beitong95/SENSELET_PLUSPLUS/Printed Circuit Board/T board/T board Schematic.png

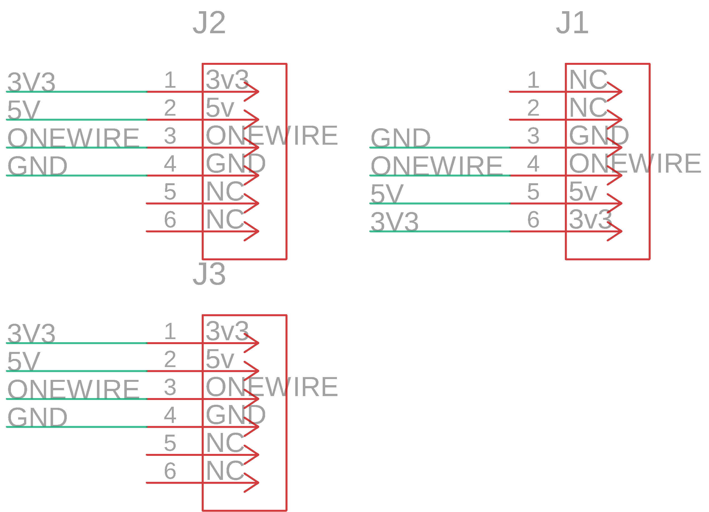
Printed Circuit Board/T board/T board Schematic.png
