beitong95/SENSELET_PLUSPLUS/3D Printed Closure/airflow sensor.png

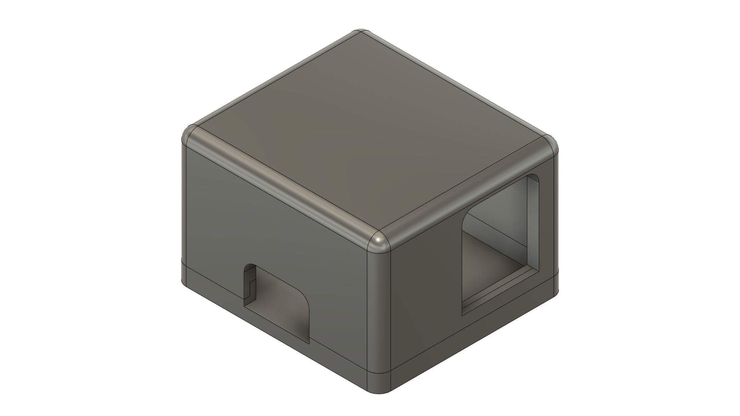
3D Printed Closure/airflow sensor.png
