beitong95/SENSELET_PLUSPLUS/3D Printed Closure/door sensor.png

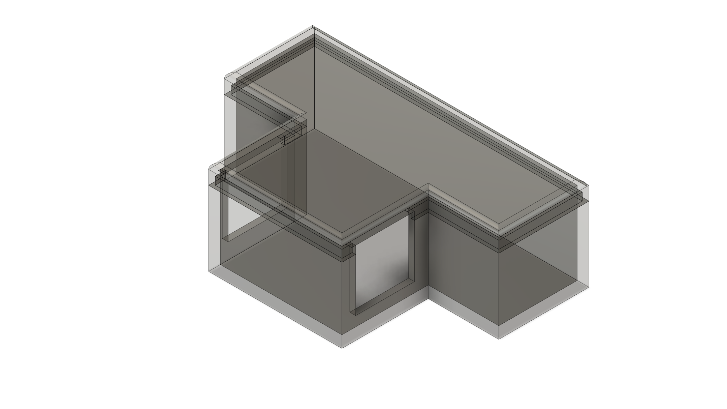
3D Printed Closure/door sensor.png
