beitong95/SENSELET_PLUSPLUS/3D Printed Closure/SenseEdge V4 with Raspberry Pi Zero W.png

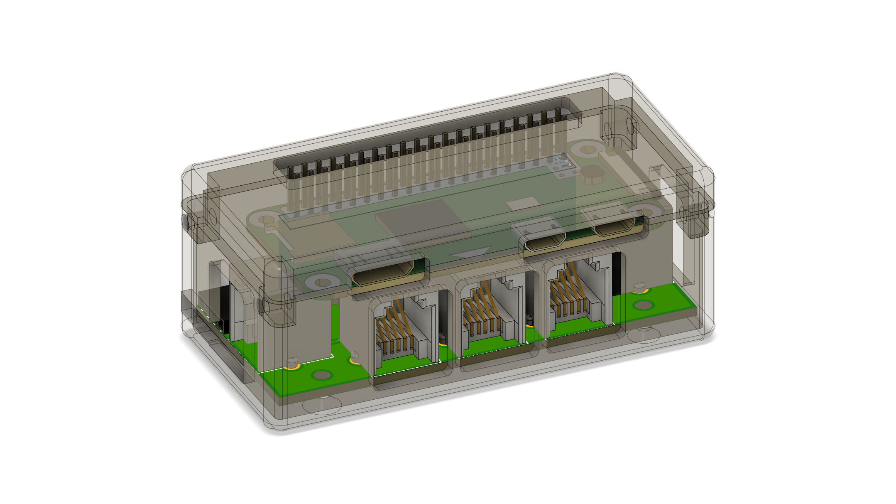
3D Printed Closure/SenseEdge V4 with Raspberry Pi Zero W.png
