beitong95/SENSELET_PLUSPLUS/3D Printed Closure/SenseEdge v4.png

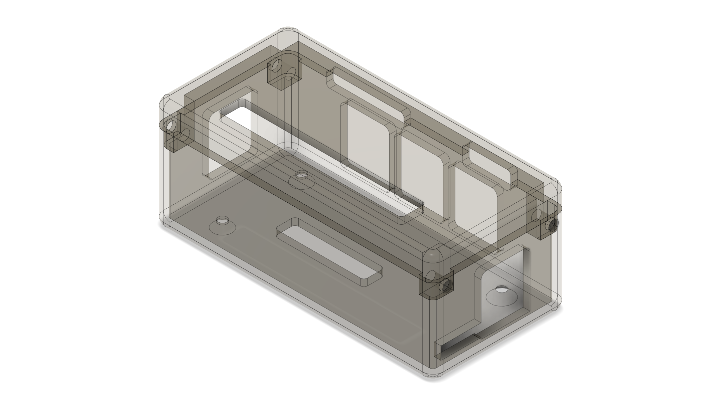
3D Printed Closure/SenseEdge v4.png
