beitong95/SENSELET_PLUSPLUS/3D Printed Closure/surface temperature sensor.png

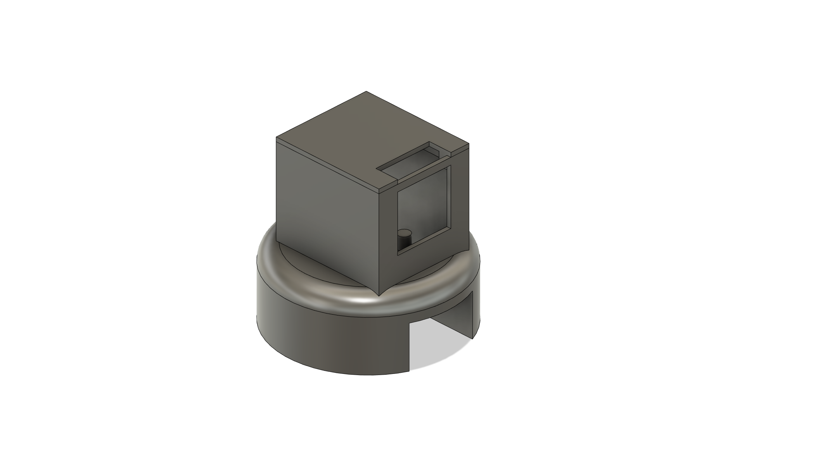
3D Printed Closure/surface temperature sensor.png
