beitong95/SENSELET_PLUSPLUS/3D Printed Closure/temperature & humidity.png

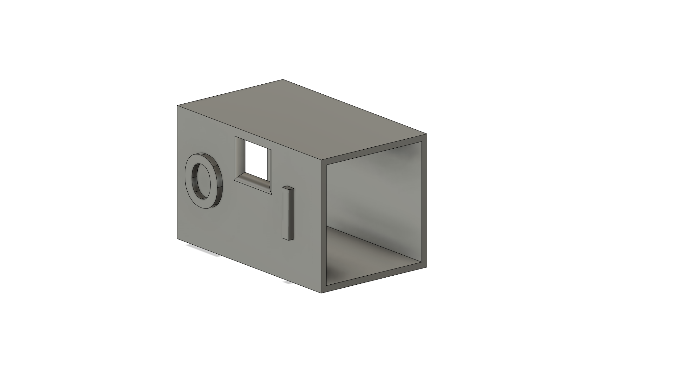
3D Printed Closure/temperature & humidity.png
