beitong95/SENSELET_PLUSPLUS/3D Printed Closure/water leakage point stand.png

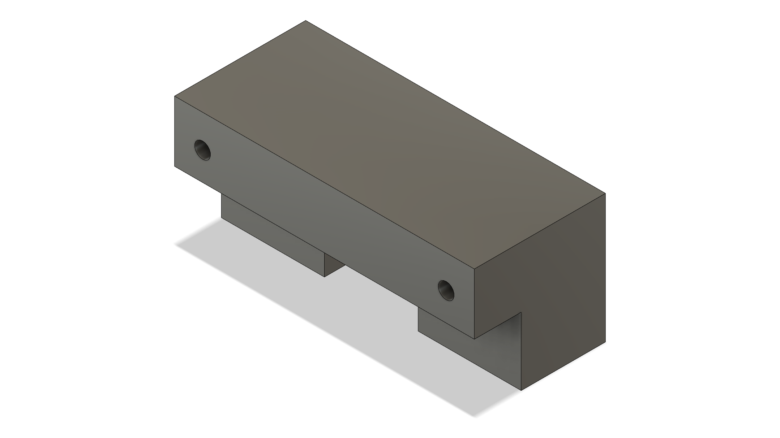
3D Printed Closure/water leakage point stand.png
