beitong95/SENSELET_PLUSPLUS/3D Printed Closure/waterleakage rope.png

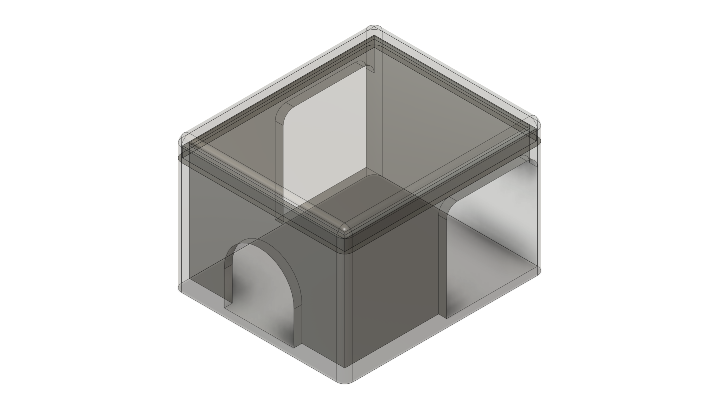
3D Printed Closure/waterleakage rope.png
