beitong95/SENSELET_PLUSPLUS/Printed Circuit Board/Airflow Sensor D6F-V/Airflow Sensor D6F-V Board Top.png

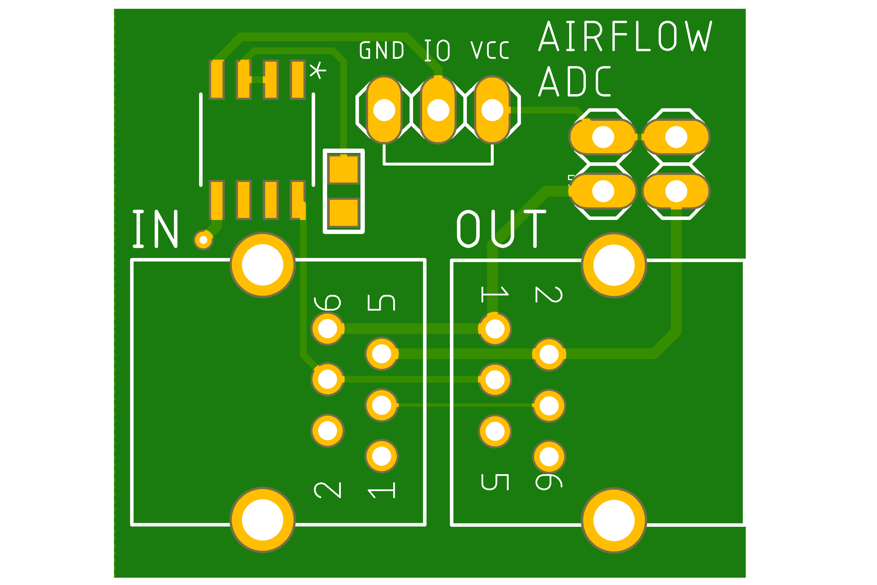
Printed Circuit Board/Airflow Sensor D6F-V/Airflow Sensor D6F-V Board Top.png
