beitong95/SENSELET_PLUSPLUS/Printed Circuit Board/Binary Output Sensor/Binary Output Sensor Board.png

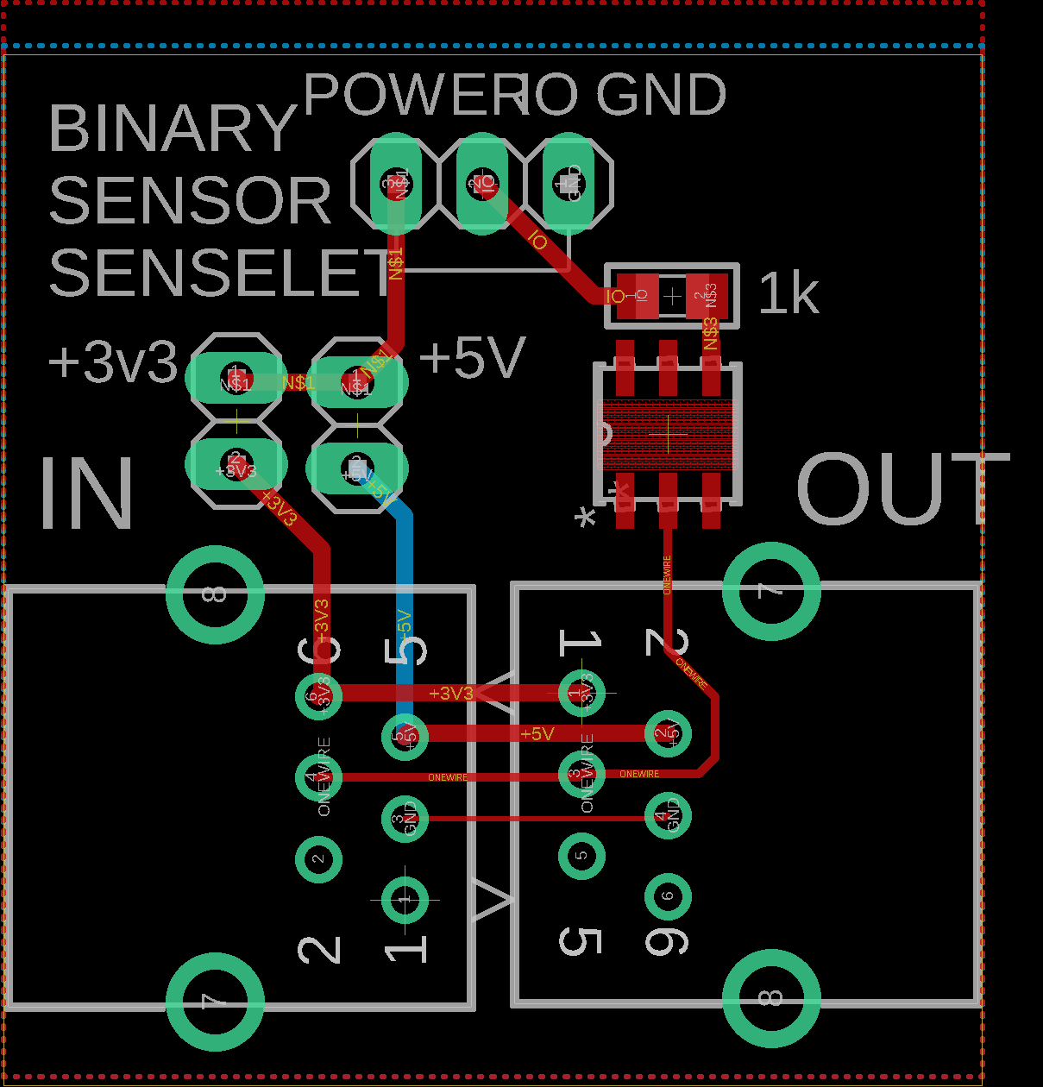
Printed Circuit Board/Binary Output Sensor/Binary Output Sensor Board.png
