beitong95/SENSELET_PLUSPLUS/Printed Circuit Board/Binary Sensor/Binary Sensor DS2413 Board.png

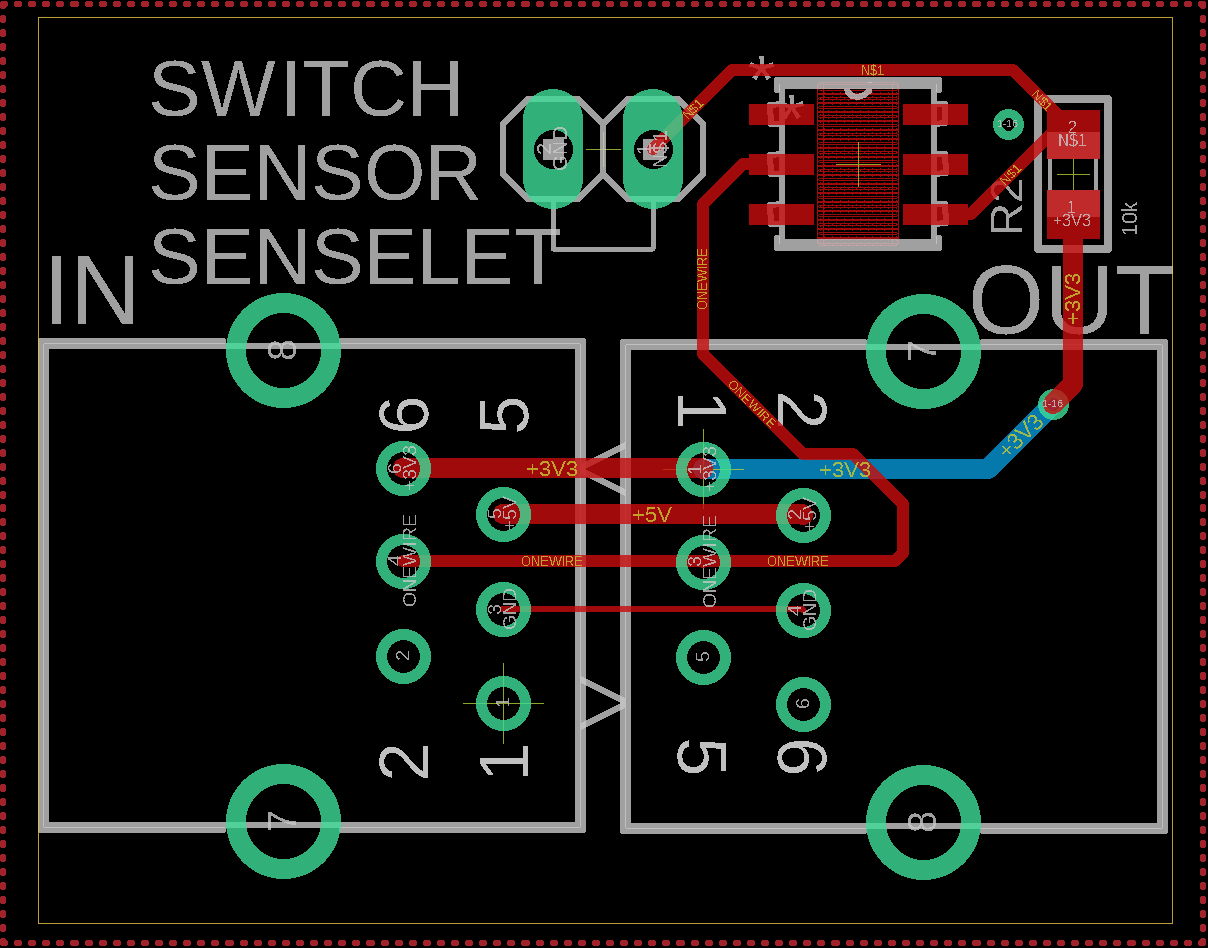
Printed Circuit Board/Binary Sensor/Binary Sensor DS2413 Board.png
