beitong95/SENSELET_PLUSPLUS/Printed Circuit Board/SenseEdge DS2482/SenseEdge Board Bottom.png

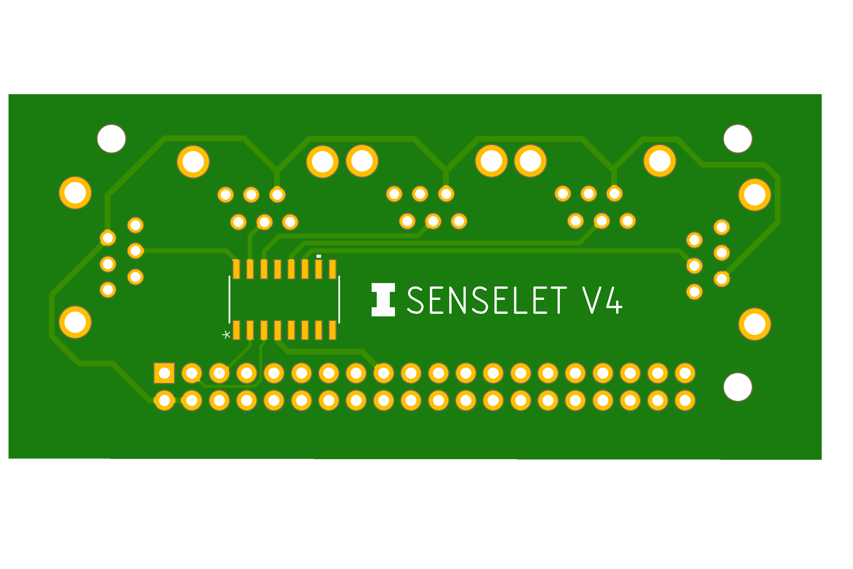
Printed Circuit Board/SenseEdge DS2482/SenseEdge Board Bottom.png
