beitong95/SENSELET_PLUSPLUS/Printed Circuit Board/SenseEdge DS2482/SenseEdge Board Top.png

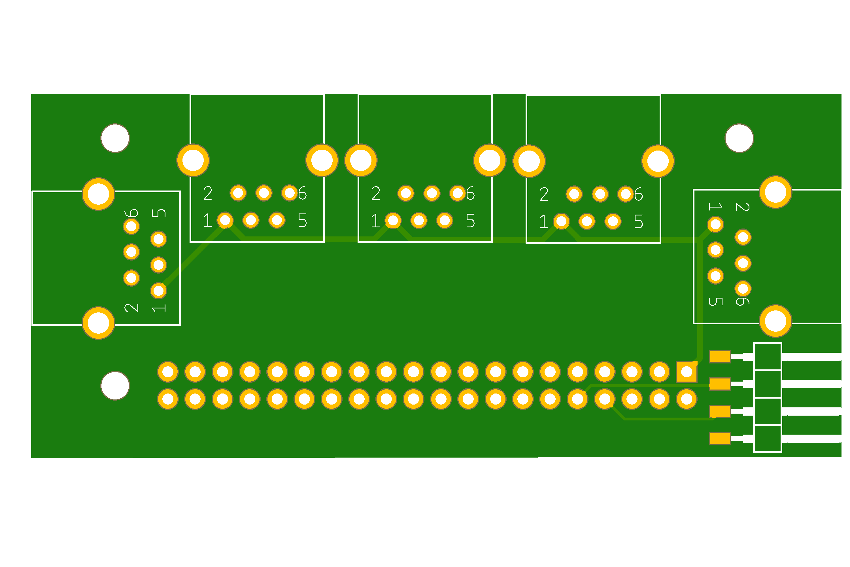
Printed Circuit Board/SenseEdge DS2482/SenseEdge Board Top.png
