beitong95/SENSELET_PLUSPLUS/Printed Circuit Board/Surface Temperature Sensor HiLetgo GY-906 MLX90614ESF/Surface Temperature Sensor DS28E17 Board.png

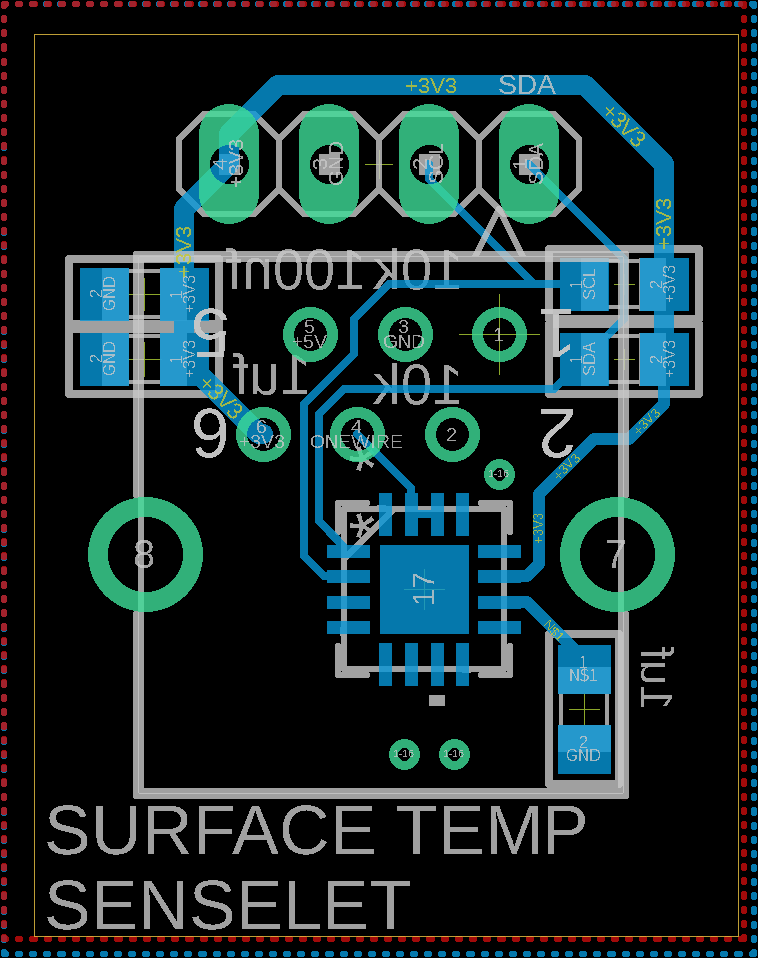
Printed Circuit Board/Surface Temperature Sensor HiLetgo GY-906 MLX90614ESF/Surface Temperature Sensor DS28E17 Board.png
