beitong95/SENSELET_PLUSPLUS/Printed Circuit Board/T board/T board Board Bottom.png

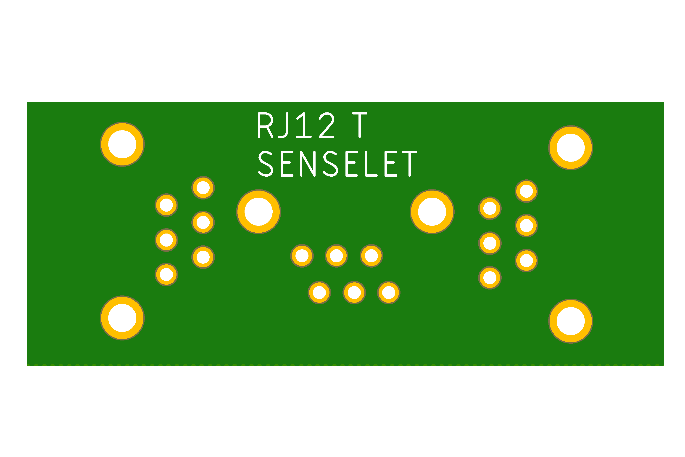
Printed Circuit Board/T board/T board Board Bottom.png
