beitong95/SENSELET_PLUSPLUS/Printed Circuit Board/T board/T board Board Top.png

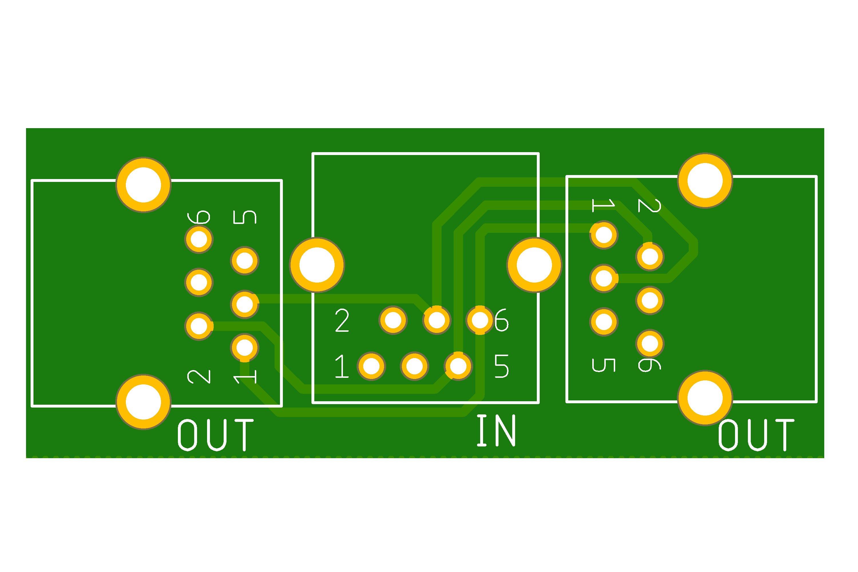
Printed Circuit Board/T board/T board Board Top.png
