beitong95/SENSELET_PLUSPLUS/Printed Circuit Board/Temperature Humidity Sensor SHT85/Temperature Humidity Sensor SHT85 Board Top.png

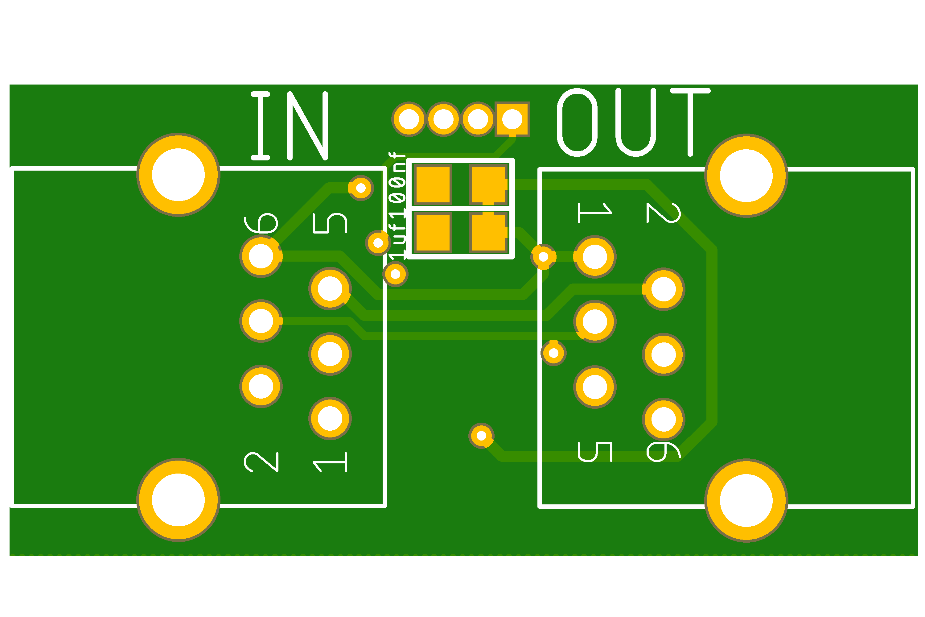
Printed Circuit Board/Temperature Humidity Sensor SHT85/Temperature Humidity Sensor SHT85 Board Top.png
