beitong95/SENSELET_PLUSPLUS/Printed Circuit Board/Water Leakage Rope Sensor RCHWES4/Water Leakage Rope Sensor RCHWES4 Board.png

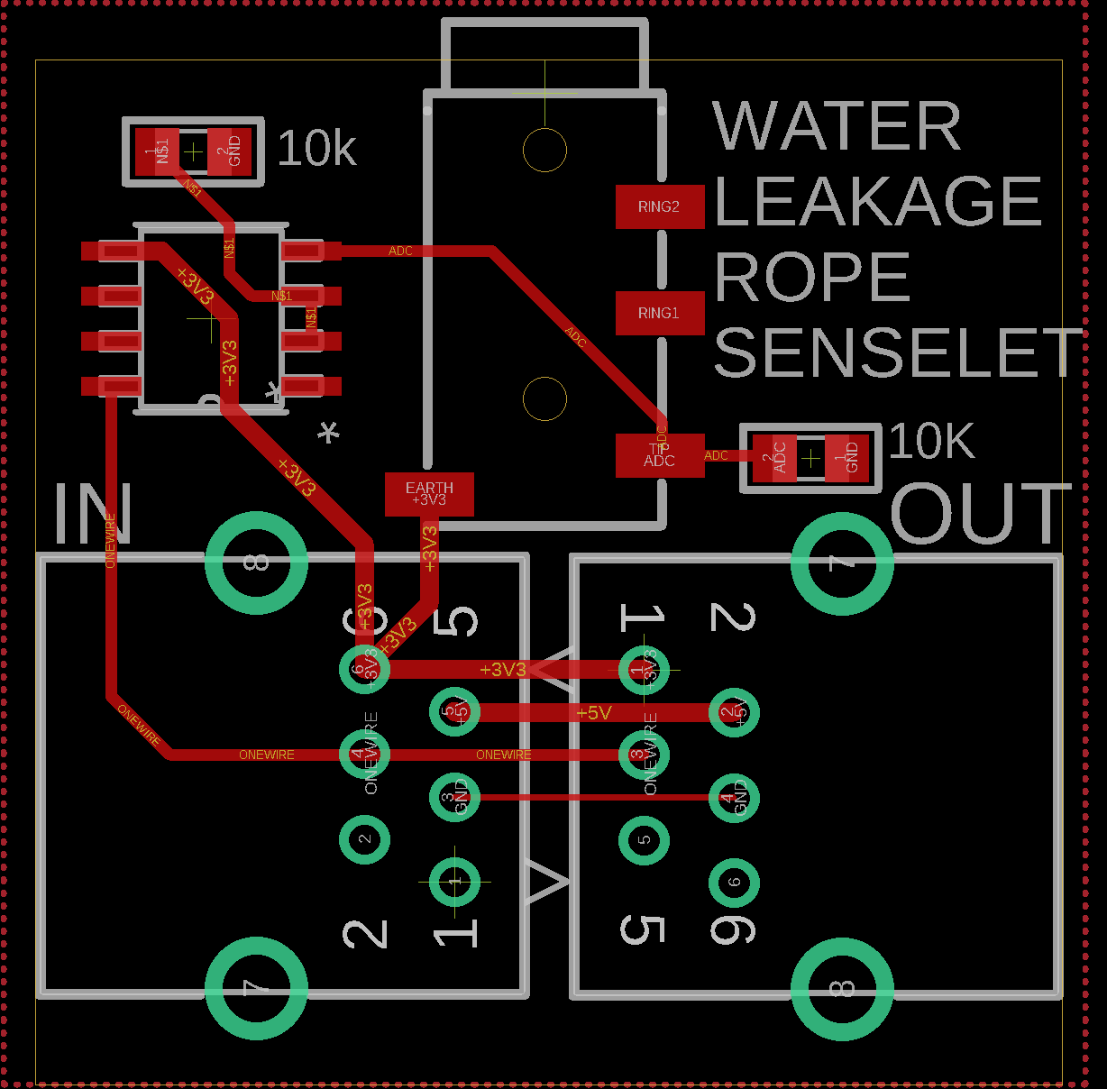
Printed Circuit Board/Water Leakage Rope Sensor RCHWES4/Water Leakage Rope Sensor RCHWES4 Board.png
