beitong95/SENSELET_PLUSPLUS/senselet++Onewire_Sensor/sensorMetaData.py

# a sample of metadata
sensorMetaData = {
            "xx-xxxxxxxxxxx": {
                    "protocol": "I2C",
                    "name": "sht85",
                    "frequency": 1,
                    "calibration": 1.921
                }, 
            "xx-xxxxxxxxxxx": {
                    "protocol": "I2C",
                    "name": "mlx90614",
                    "frequency": 1
                }, 
            "xx-xxxxxxxxxxx": {
                    "protocol": "ADC",
                    "name": "waterLeakageRope",
                    "frequency":1
                }, 
            "xx-xxxxxxxxxxx": {
                    "protocol": "ADC",
                    "name": "airFlow",
                    "frequency":1
                }, 
            "xx-xxxxxxxxxxx": {
                    "protocol": "GPIO",
                    "name": "waterLeakagePoint",
                    "frequency":1
                }, 
            "xx-xxxxxxxxxxx": {
                    "protocol": "GPIO",
                    "name": "doorSensorSmall",
                    "frequency":1
                }, 
	    "openweather_sensor_1": {
		    "name": "openweather_sensor"
		}
        }
